sowbug/weblight/hardware/mfg/production/0.9.2/bottom.png

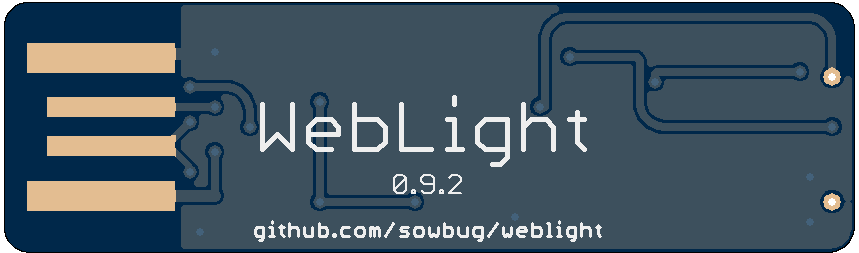
hardware/mfg/production/0.9.2/bottom.png
