sowbug/weblight/hardware/mfg/production/0.9.2/bottom_copper.png

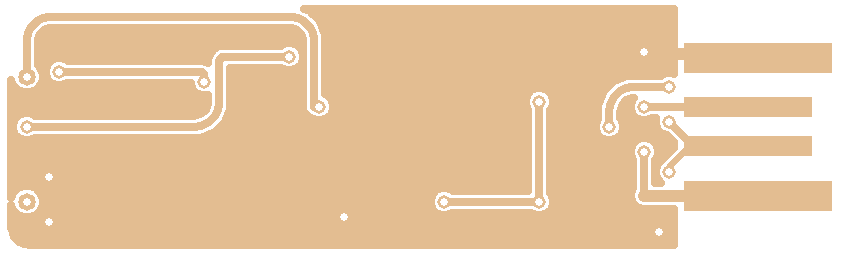
hardware/mfg/production/0.9.2/bottom_copper.png
