sowbug/weblight/hardware/mfg/production/0.9.2/schematic.png

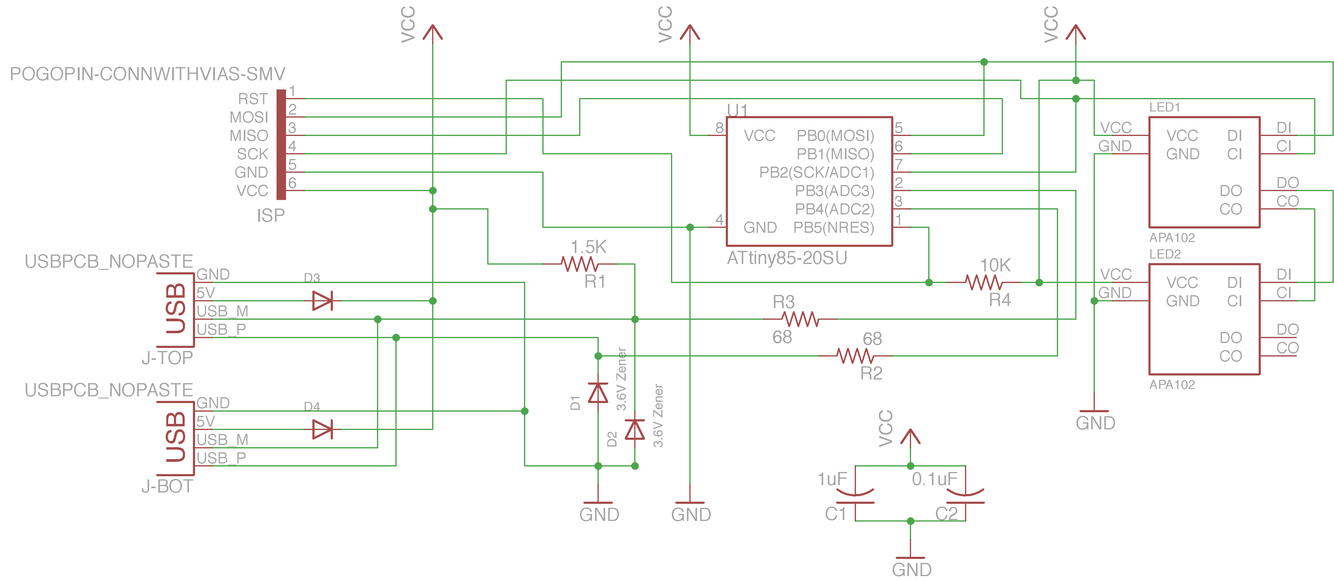
hardware/mfg/production/0.9.2/schematic.png
