sowbug/weblight/hardware/mfg/production/1.0-rc1/board.png

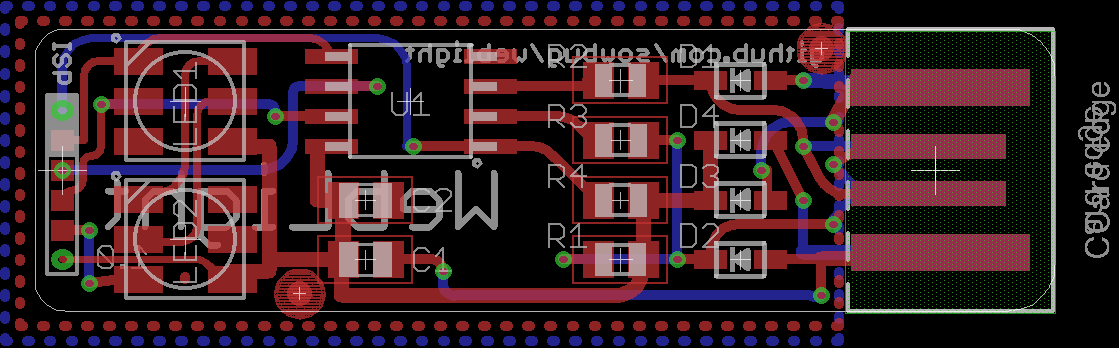
hardware/mfg/production/1.0-rc1/board.png
