sowbug/weblight/hardware/mfg/production/1.0-rc1/bottom.png

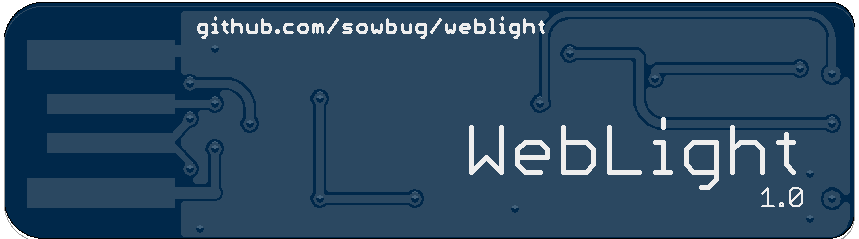
hardware/mfg/production/1.0-rc1/bottom.png
