sowbug/weblight/hardware/mfg/production/1.0-rc1/panelized_3x10/wl_1.0_Combined_Top.png

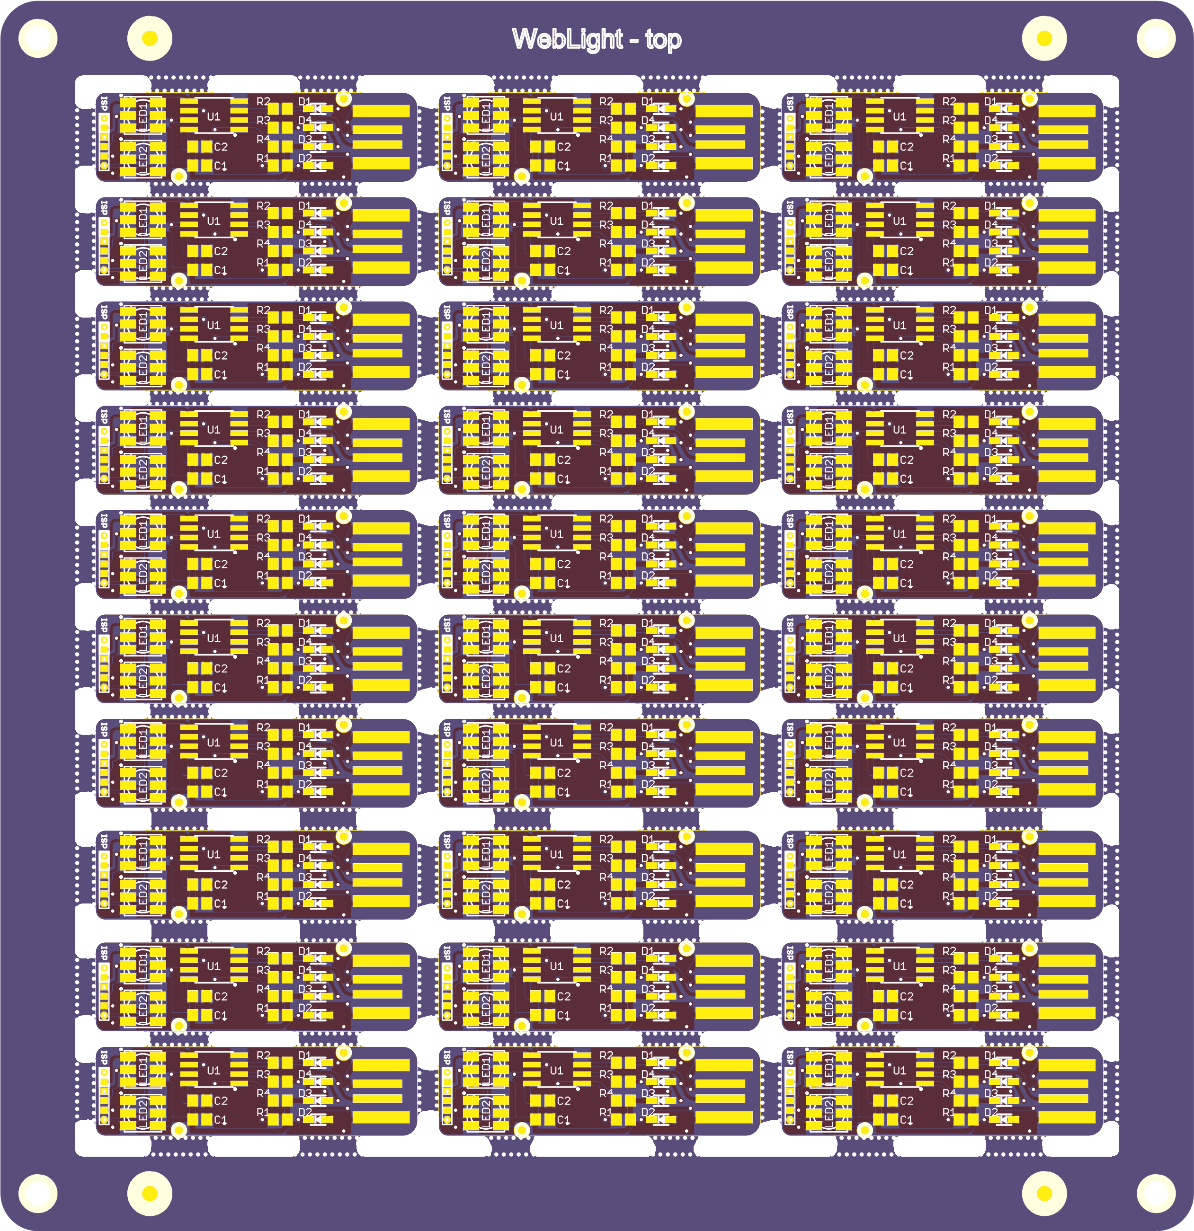
hardware/mfg/production/1.0-rc1/panelized_3x10/wl_1.0_Combined_Top.png
