sowbug/weblight/hardware/mfg/production/1.0-rc1/schematic.png

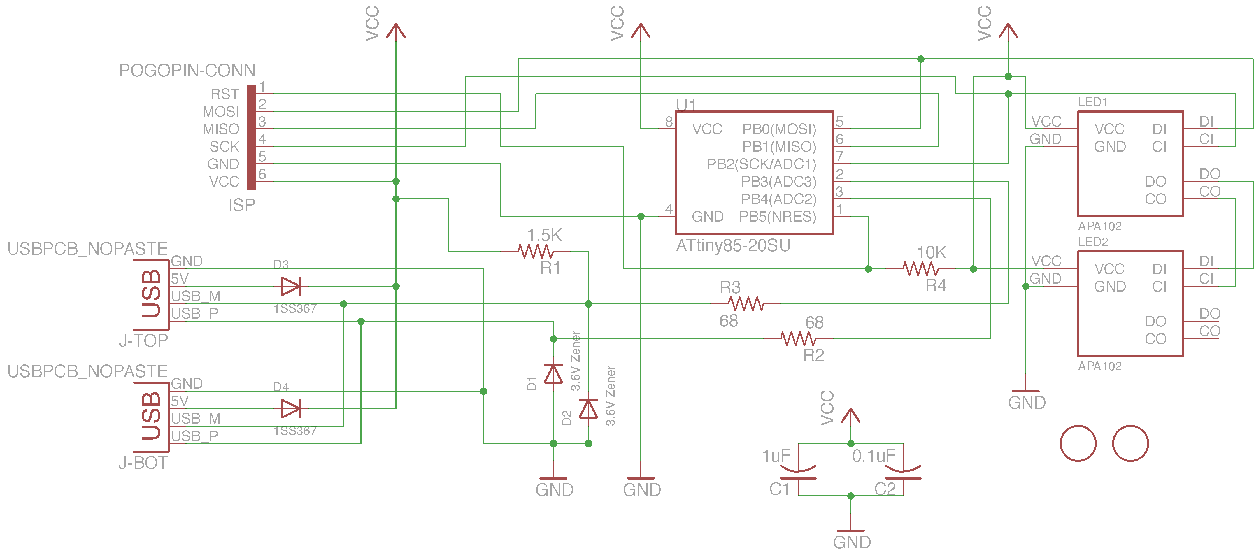
hardware/mfg/production/1.0-rc1/schematic.png
