sowbug/weblight/hardware/mfg/production/1.0-rc1/top.png

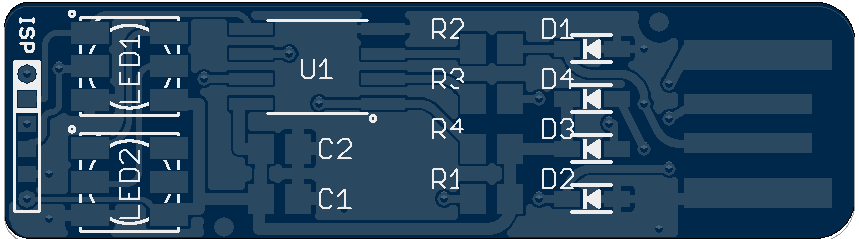
hardware/mfg/production/1.0-rc1/top.png
