sowbug/weblight/hardware/mfg/production/1.0-rc1/top_silkscreen.png

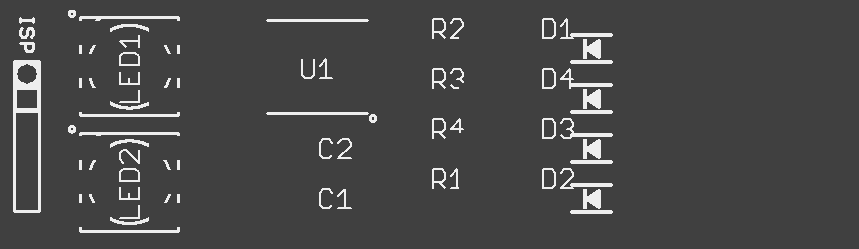
hardware/mfg/production/1.0-rc1/top_silkscreen.png
