sowbug/weblight/hardware/mfg/production/145x140_frame/wl_frame_Combined_Bottom.png

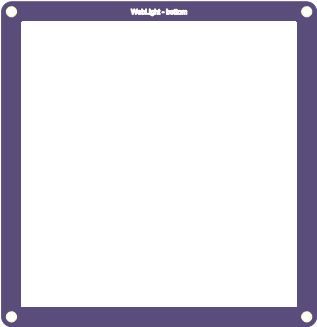
hardware/mfg/production/145x140_frame/wl_frame_Combined_Bottom.png
