sowbug/weblight/hardware/ws2812/mfg/developer/0.0.1/board.png

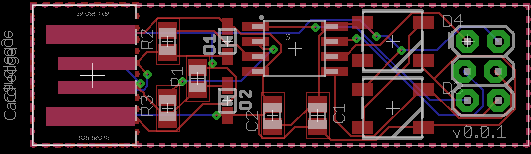
hardware/ws2812/mfg/developer/0.0.1/board.png
