sowbug/weblight/hardware/ws2812/mfg/developer/0.0.1/schematic.png

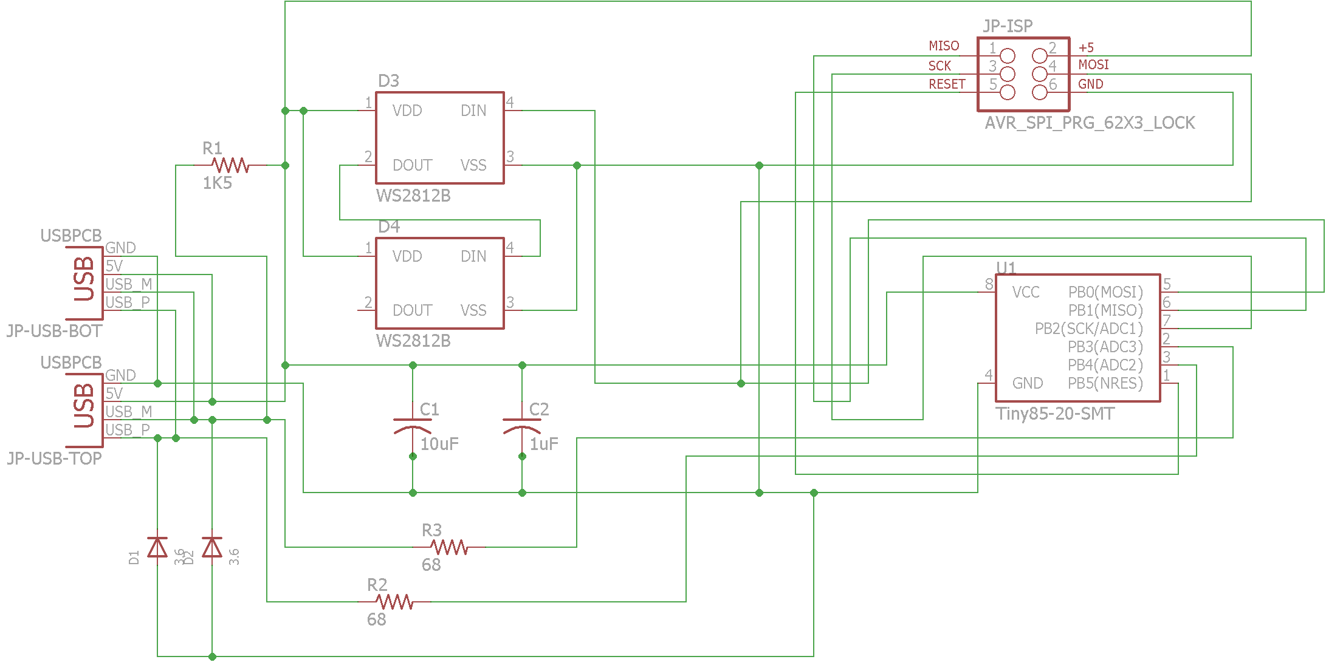
hardware/ws2812/mfg/developer/0.0.1/schematic.png
