sowbug/weblight/img/IMG_20151021_104450.jpg

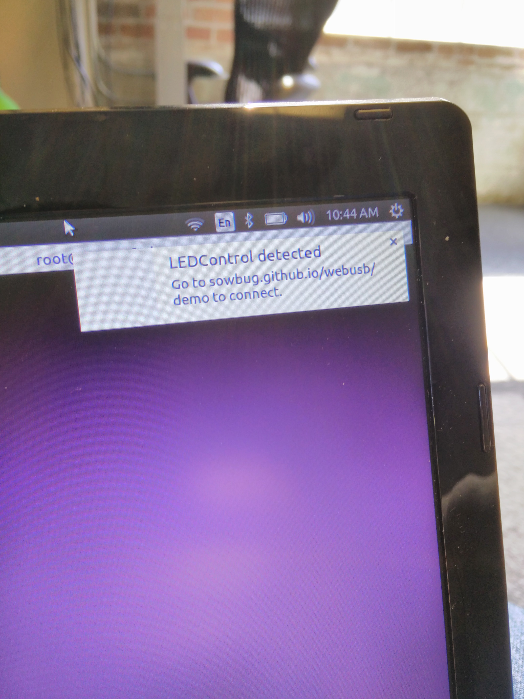
img/IMG_20151021_104450.jpg
