sowbug/weblight/img/IMG_20151021_141538.jpg

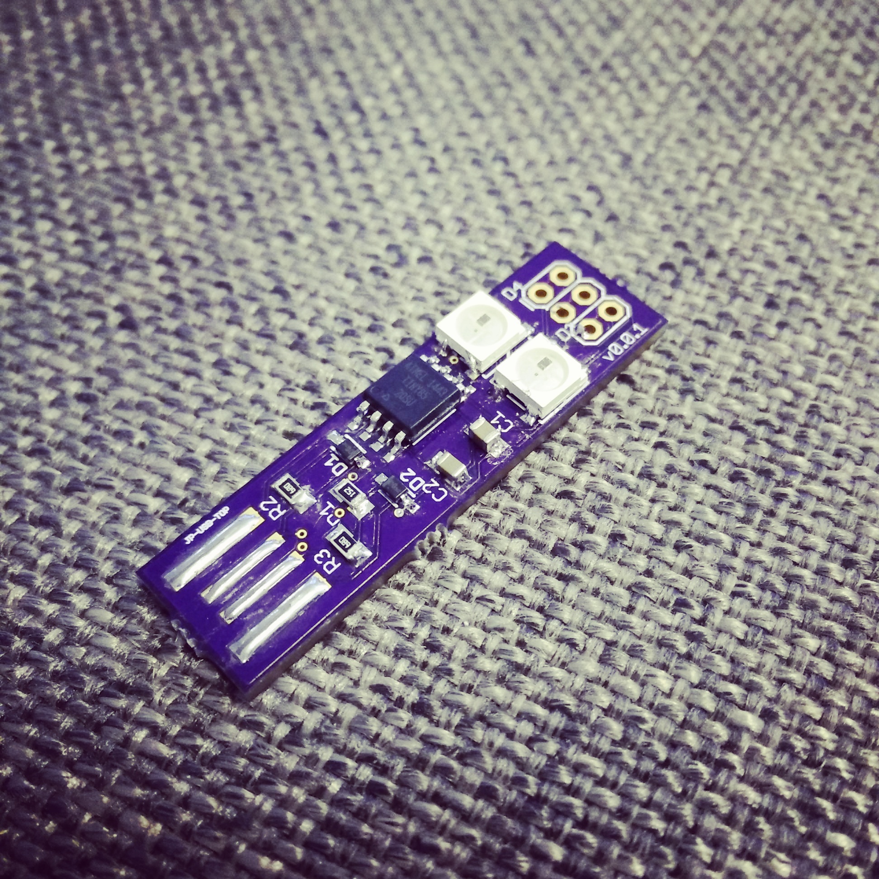
img/IMG_20151021_141538.jpg
