sowbug/weblight/img/IMG_20151111_091258.jpg

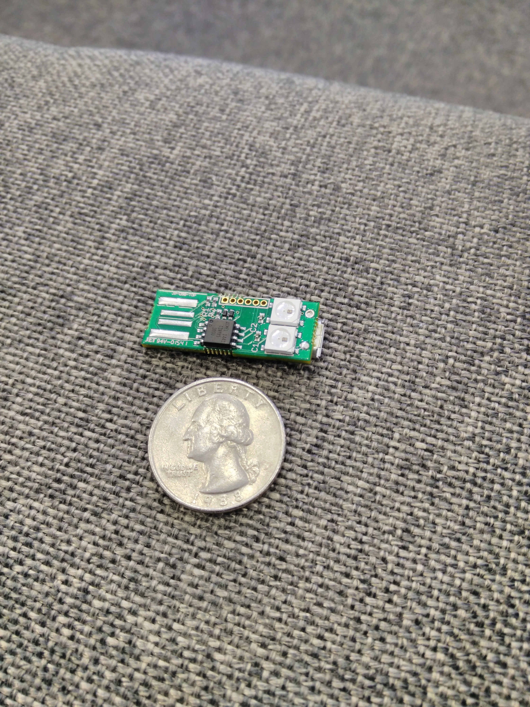
img/IMG_20151111_091258.jpg
