sowbug/weblight/img/IMG_20151111_091258_sq.jpg

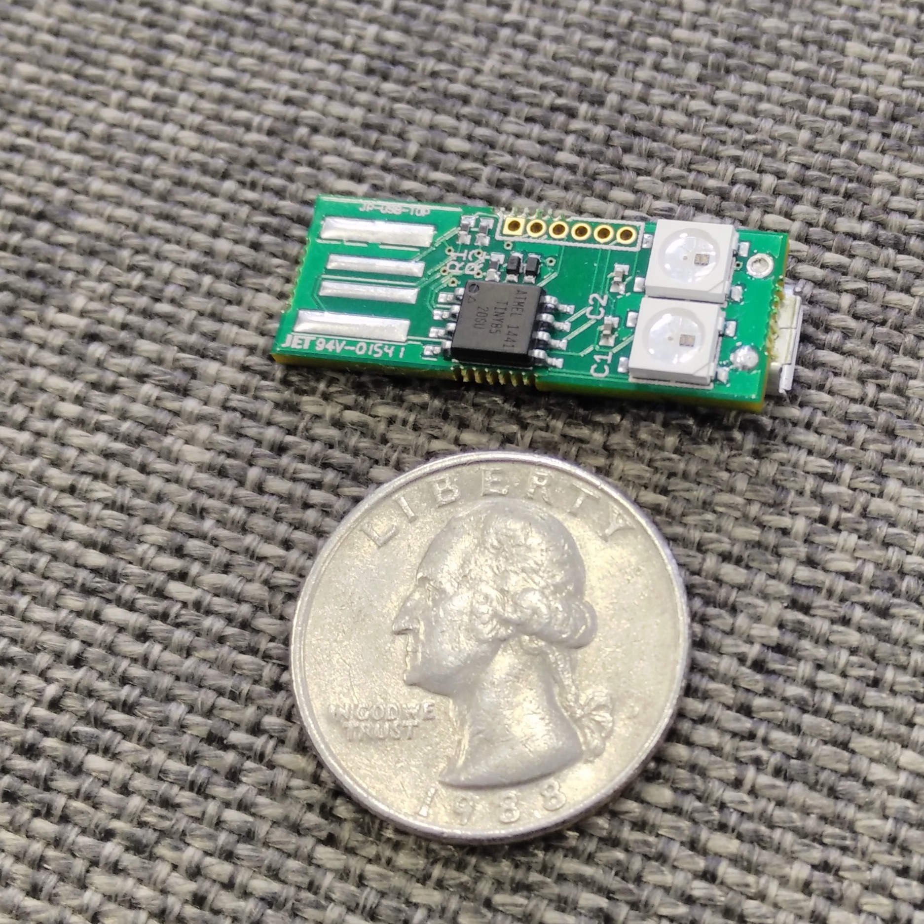
img/IMG_20151111_091258_sq.jpg
