sowbug/weblight/img/IMG_20151116_182820.jpg

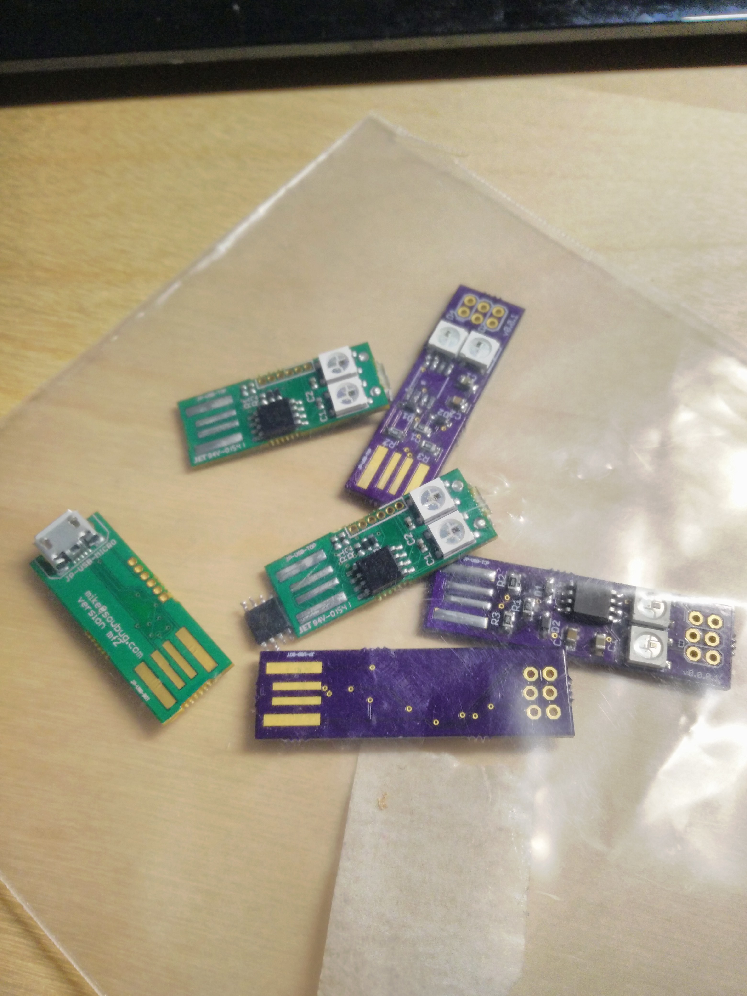
img/IMG_20151116_182820.jpg
