sowbug/weblight/img/IMG_20151206_175501.jpg

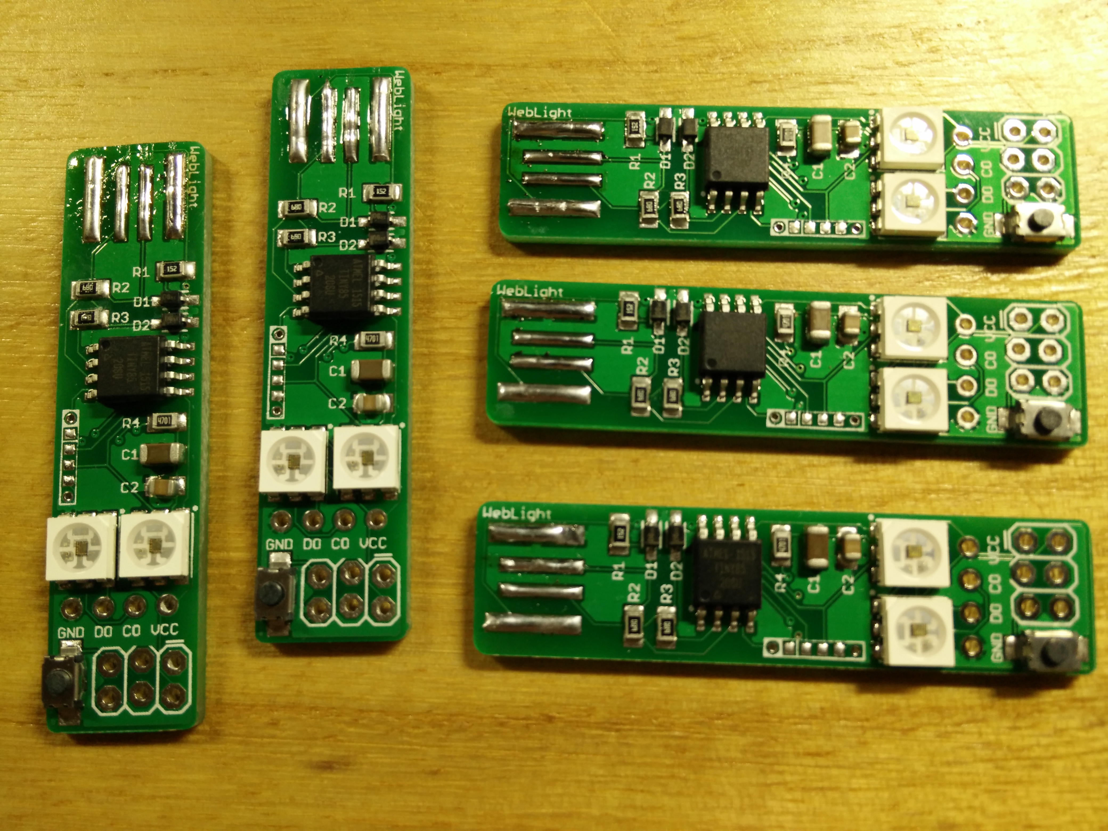
img/IMG_20151206_175501.jpg
