sowbug/weblight/img/IMG_20151206_175501_sq.jpg

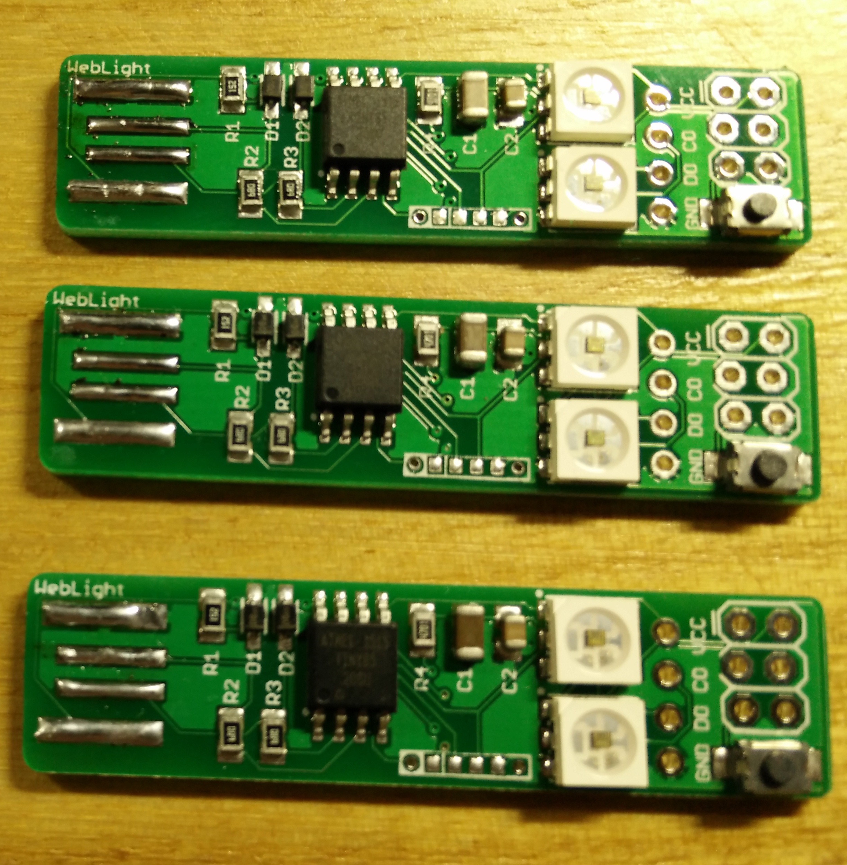
img/IMG_20151206_175501_sq.jpg
