sowbug/weblight/refs/adafruit_products_trinket5.png

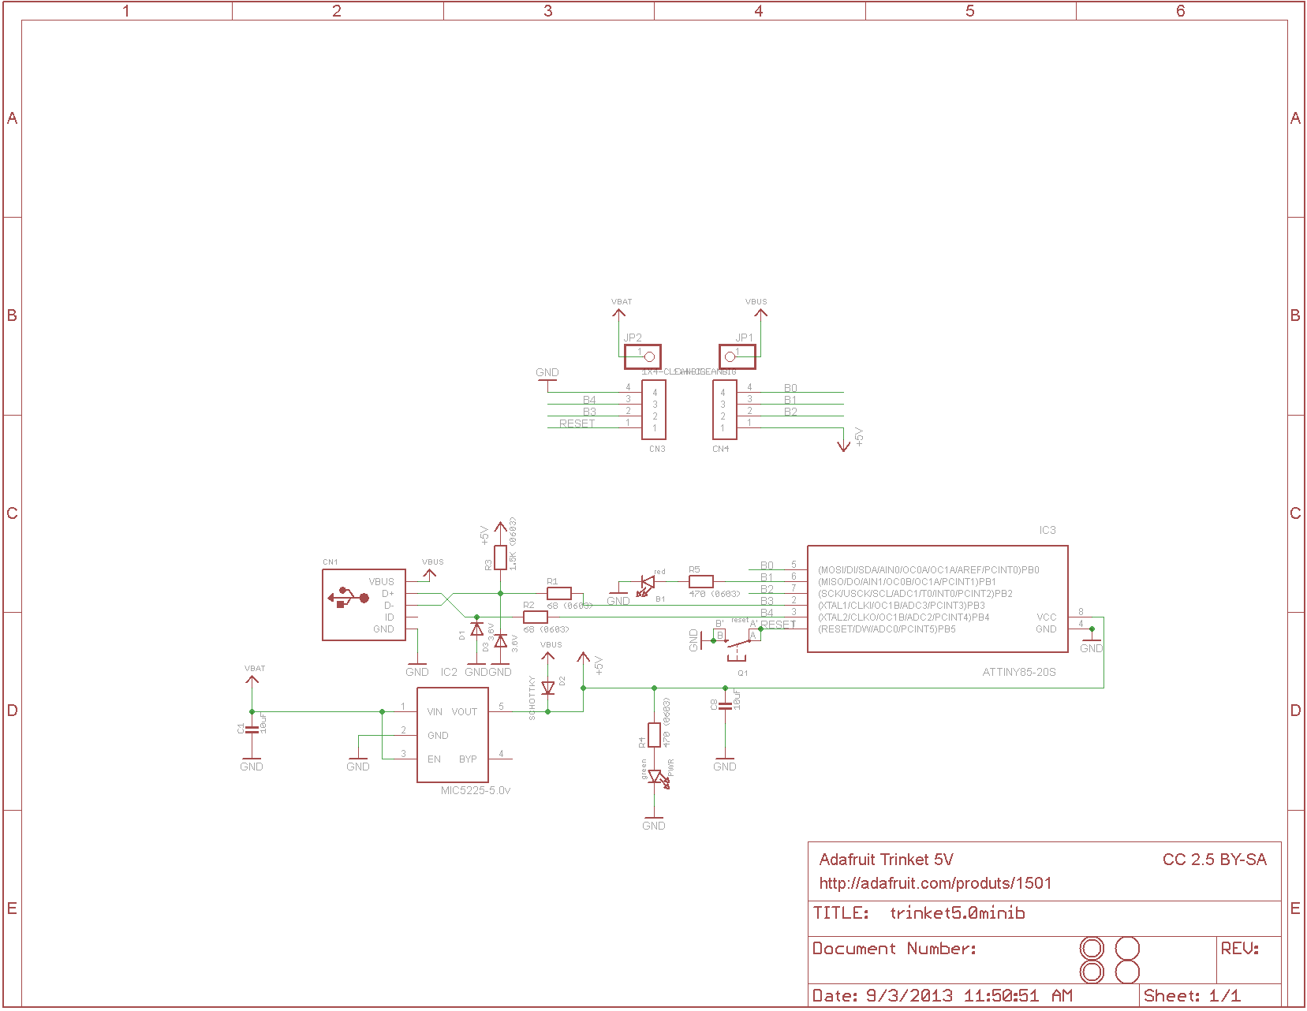
refs/adafruit_products_trinket5.png
