sowbug/weblight/hardware/mfg/production/0.9.2/bottom_soldermask.png

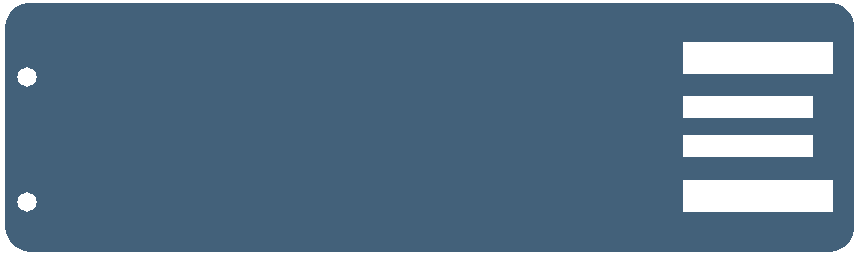
hardware/mfg/production/0.9.2/bottom_soldermask.png
