sowbug/weblight/hardware/mfg/production/1.0-rc1/bottom_soldermask.png

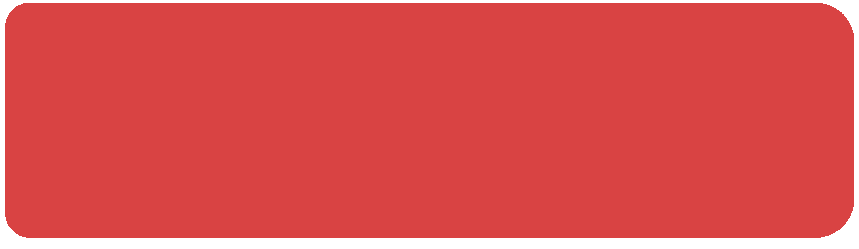
hardware/mfg/production/1.0-rc1/bottom_soldermask.png
