sowbug/weblight/firmware/app.h

// Copyright 2015 Mike Tsao
//
// WebLight firmware
// https://github.com/sowbug/weblight

#if !defined(__APP_H__)
#define __APP_H_

typedef struct {
} App;

void AppInit(App *ctx);
void AppRun(App *ctx);

#endif  // #if !defined(__APP_H__)
